Vincent-Therrien/ELE3000/appareil/demo1.jpg

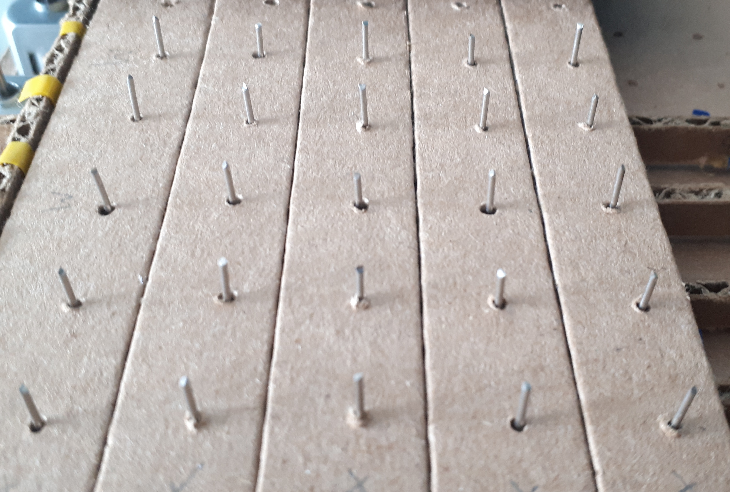
appareil/demo1.jpg
