Vincent-Therrien/ELE3000/appareil/demo2.jpg

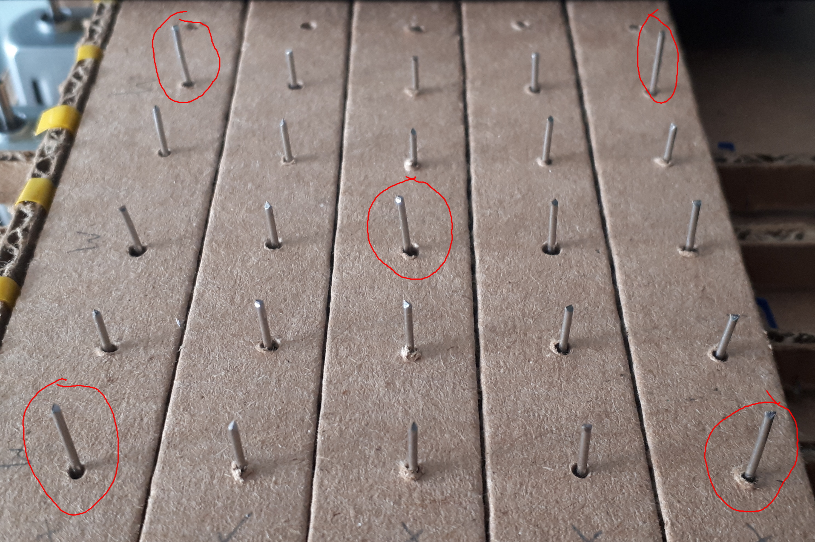
appareil/demo2.jpg
