Vincent-Therrien/ELE3000/appareil/etage1.jpg

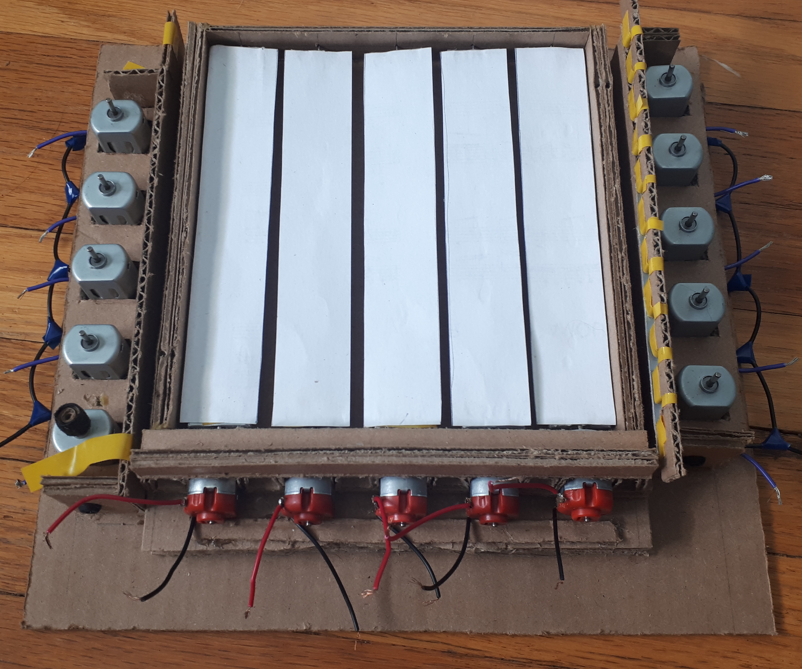
appareil/etage1.jpg
