Vincent-Therrien/ELE3000/appareil/etage2.jpg

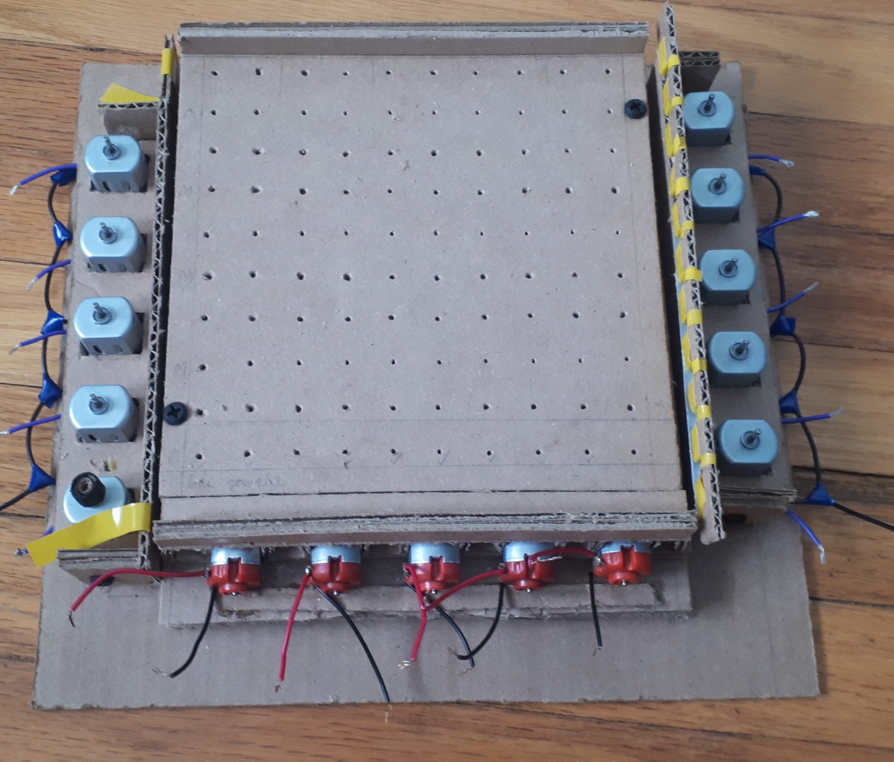
appareil/etage2.jpg
