Vincent-Therrien/ELE3000/appareil/etage3.jpg

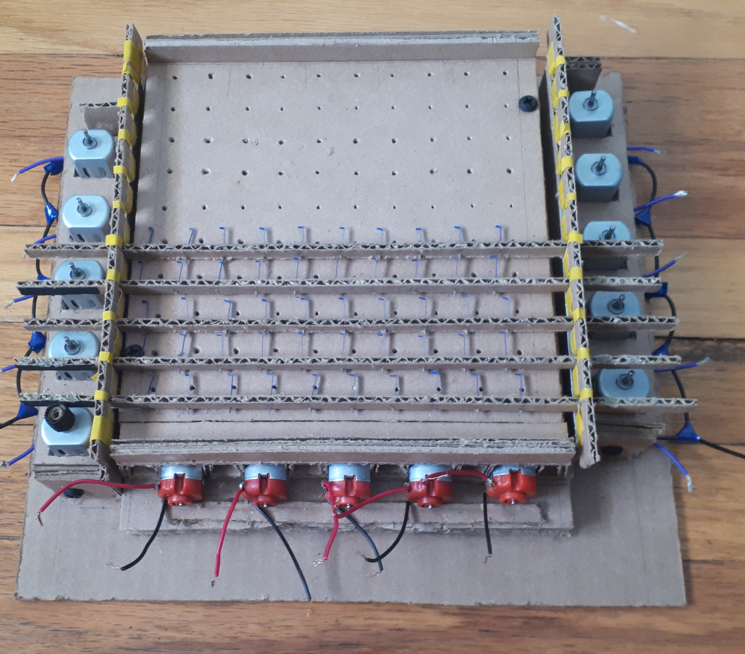
appareil/etage3.jpg
