Vincent-Therrien/ELE3000/appareil/etage4.jpg

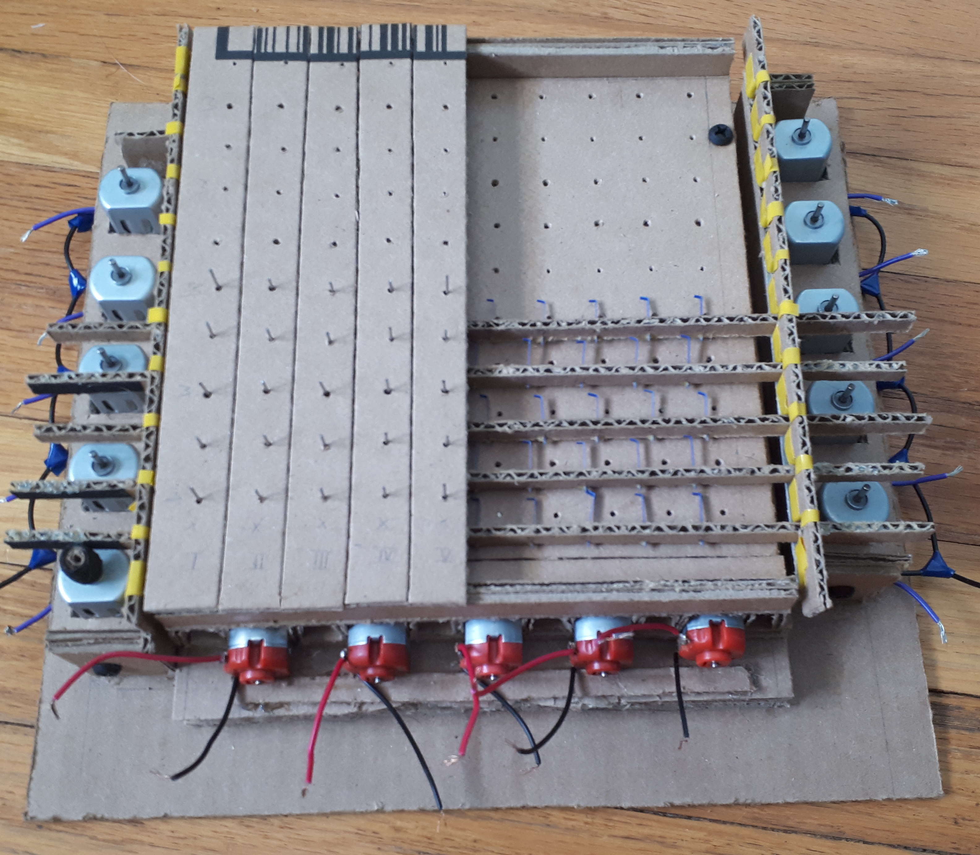
appareil/etage4.jpg
