Vincent-Therrien/ELE3000/html/_images/dimensions.png

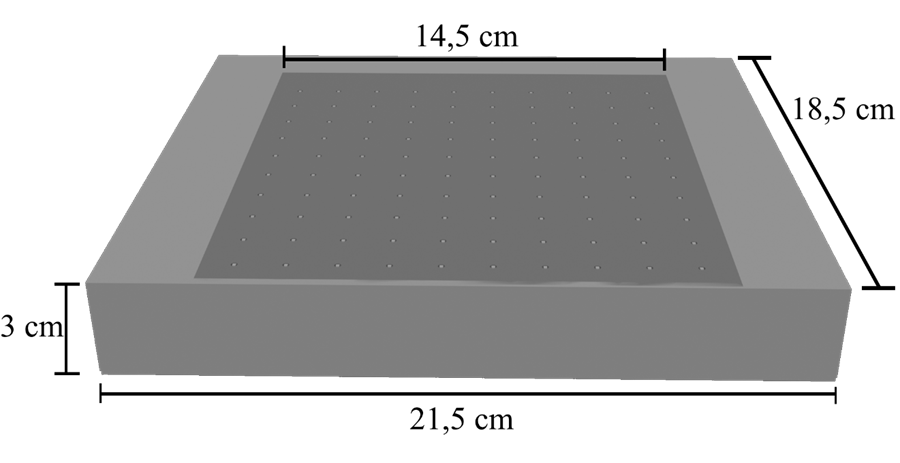
html/_images/dimensions.png
