Vincent-Therrien/ELE3000/html/_images/hyperbraille.PNG

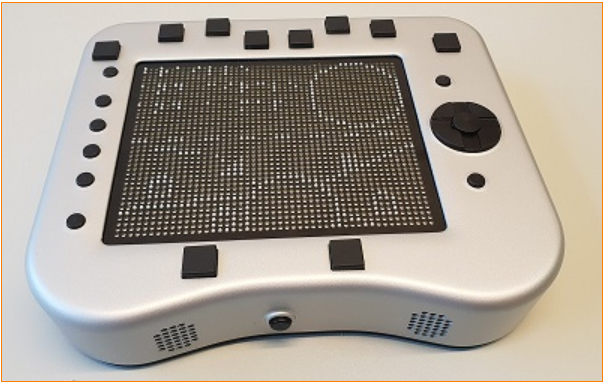
html/_images/hyperbraille.PNG
