Vincent-Therrien/ELE3000/html/_images/m1.png

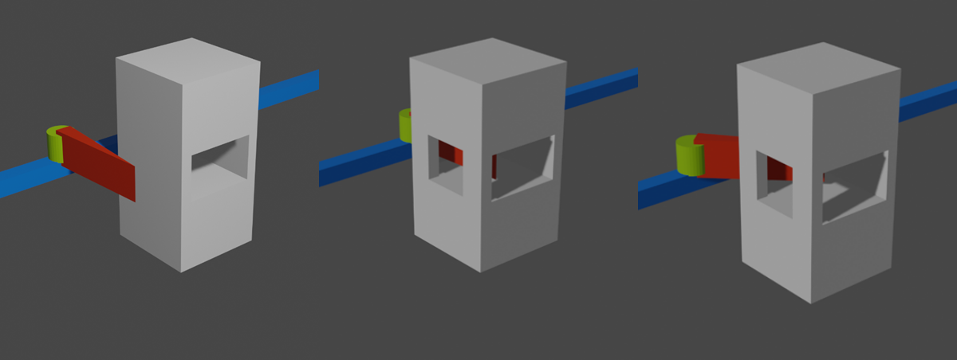
html/_images/m1.png
