Vincent-Therrien/ELE3000/html/_images/OModhrain.PNG

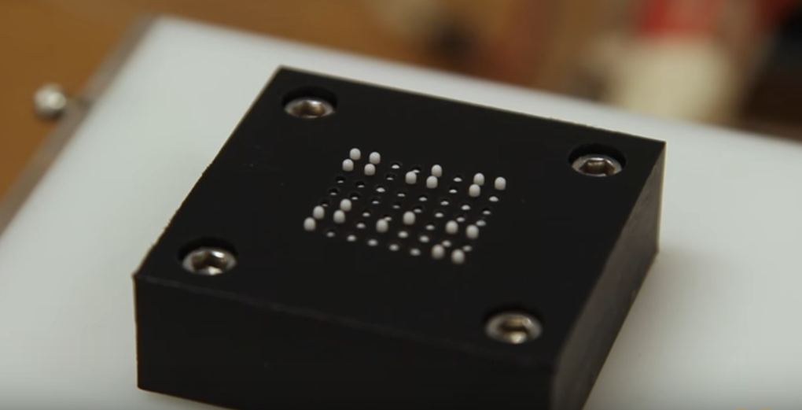
html/_images/OModhrain.PNG
