Vincent-Therrien/ELE3000/html/_images/PCB.png

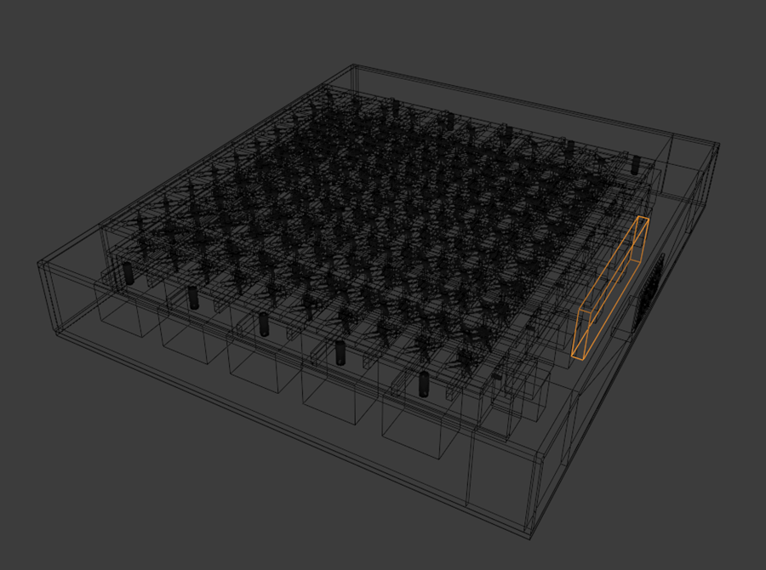
html/_images/PCB.png
