Vincent-Therrien/ELE3000/html/_images/prise.png

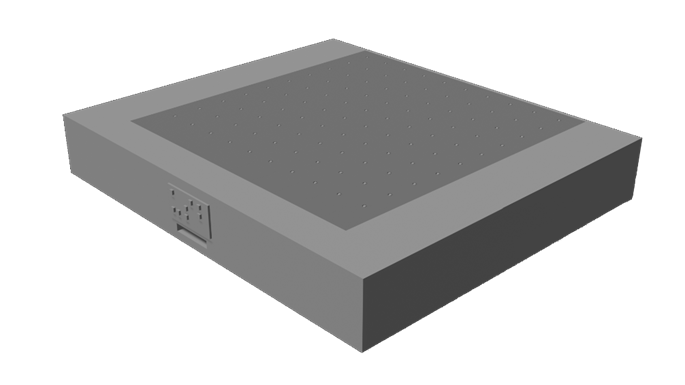
html/_images/prise.png
