Vincent-Therrien/ELE3000/html/_images/tiges.png

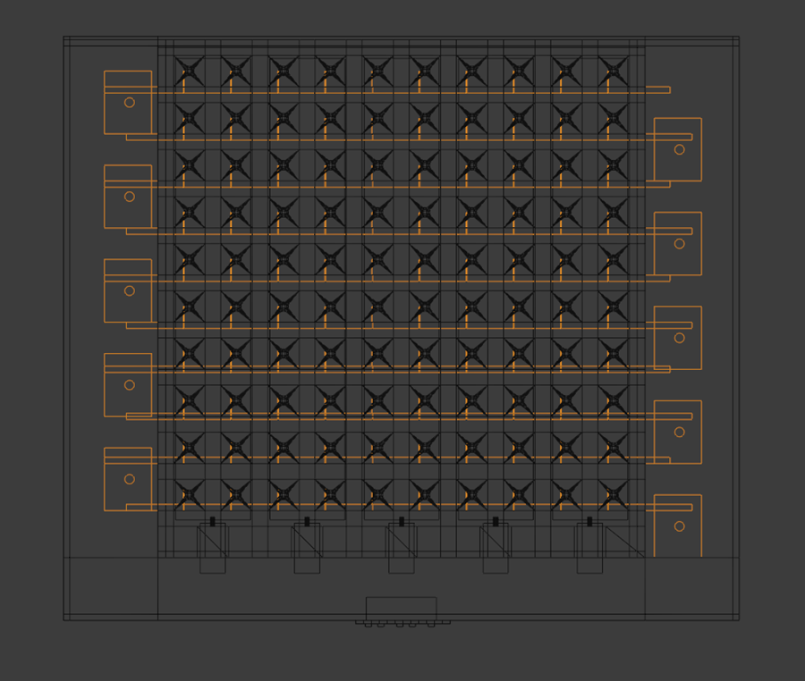
html/_images/tiges.png
