Vincent-Therrien/ELE3000/html/_images/Zhang.PNG

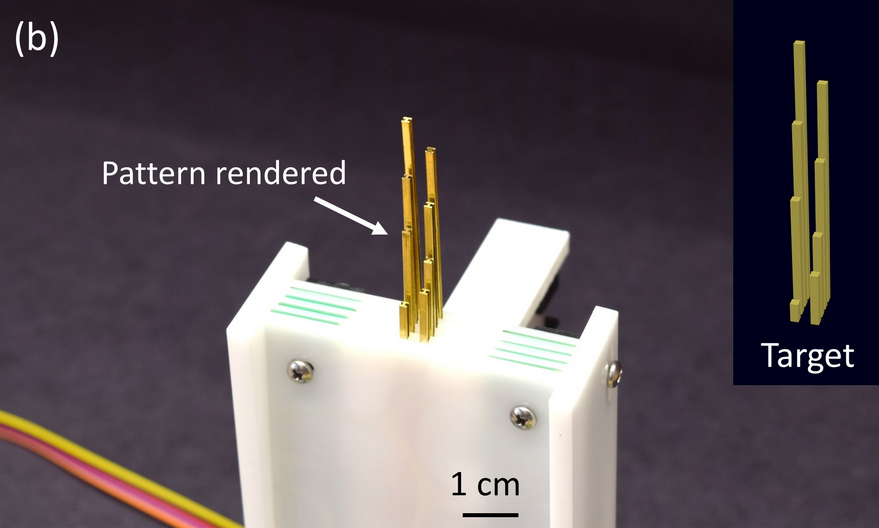
html/_images/Zhang.PNG
